Nonuwastaken/Audio_Visualizer/Custom_PCB/20260926_110037.jpg

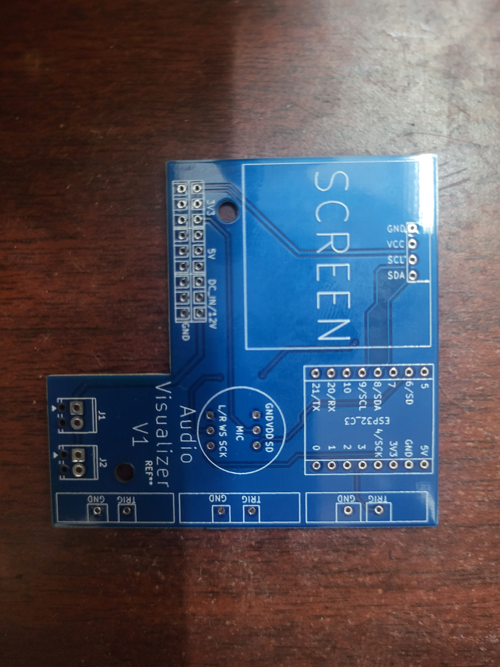
Custom_PCB/20260926_110037.jpg
